NKTKLN/eink-environment-clock/firmware/src/epd_font5x7.h

/*
 * Classic 5x7 fixed-width bitmap font from Adafruit-GFX (glcdfont.c),
 * the same font the original Arduino sketch used. Each glyph is 5 column
 * bytes, bit 0 = top row. Index 95 is the degree sign.
 */
#pragma once

#include <stdint.h>

#define FONT5X7_DEGREE_INDEX 95

static const uint8_t font5x7[96][5] = {
    { 0x00, 0x00, 0x00, 0x00, 0x00 }, /*   */
    { 0x00, 0x00, 0x5F, 0x00, 0x00 }, /* ! */
    { 0x00, 0x07, 0x00, 0x07, 0x00 }, /* " */
    { 0x14, 0x7F, 0x14, 0x7F, 0x14 }, /* # */
    { 0x24, 0x2A, 0x7F, 0x2A, 0x12 }, /* $ */
    { 0x23, 0x13, 0x08, 0x64, 0x62 }, /* % */
    { 0x36, 0x49, 0x56, 0x20, 0x50 }, /* & */
    { 0x00, 0x08, 0x07, 0x03, 0x00 }, /* ' */
    { 0x00, 0x1C, 0x22, 0x41, 0x00 }, /* ( */
    { 0x00, 0x41, 0x22, 0x1C, 0x00 }, /* ) */
    { 0x2A, 0x1C, 0x7F, 0x1C, 0x2A }, /* asterisk */
    { 0x08, 0x08, 0x3E, 0x08, 0x08 }, /* + */
    { 0x00, 0x80, 0x70, 0x30, 0x00 }, /* , */
    { 0x08, 0x08, 0x08, 0x08, 0x08 }, /* - */
    { 0x00, 0x00, 0x60, 0x60, 0x00 }, /* . */
    { 0x20, 0x10, 0x08, 0x04, 0x02 }, /* / */
    { 0x3E, 0x51, 0x49, 0x45, 0x3E }, /* 0 */
    { 0x00, 0x42, 0x7F, 0x40, 0x00 }, /* 1 */
    { 0x72, 0x49, 0x49, 0x49, 0x46 }, /* 2 */
    { 0x21, 0x41, 0x49, 0x4D, 0x33 }, /* 3 */
    { 0x18, 0x14, 0x12, 0x7F, 0x10 }, /* 4 */
    { 0x27, 0x45, 0x45, 0x45, 0x39 }, /* 5 */
    { 0x3C, 0x4A, 0x49, 0x49, 0x31 }, /* 6 */
    { 0x41, 0x21, 0x11, 0x09, 0x07 }, /* 7 */
    { 0x36, 0x49, 0x49, 0x49, 0x36 }, /* 8 */
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
    { 0x44, 0x64, 0x54, 0x4C, 0x44 }, /* z */
    { 0x00, 0x08, 0x36, 0x41, 0x00 }, /* { */
    { 0x00, 0x00, 0x77, 0x00, 0x00 }, /* | */
    { 0x00, 0x41, 0x36, 0x08, 0x00 }, /* } */
    { 0x02, 0x01, 0x02, 0x04, 0x02 }, /* ~ */
    { 0x06, 0x0F, 0x09, 0x0F, 0x06 }, /* degree */
};
