NKTKLN/eink-environment-clock/firmware/src/net_time.c

#include "net_time.h"

#include <stdatomic.h>
#include <string.h>

#include "esp_event.h"
#include "esp_log.h"
#include "esp_netif.h"
#include "esp_sntp.h"
#include "esp_wifi.h"
#include "nvs_flash.h"

#include "app_config.h"

static const char *TAG = "net_time";

static atomic_bool s_synced;
static bool s_sntp_started;

static void on_time_sync(struct timeval *tv)
{
    (void)tv;
    ESP_LOGI(TAG, "time synchronized via SNTP");
    atomic_store(&s_synced, true);
}

static void start_sntp_once(void)
{
    if (s_sntp_started) {
        return;
    }
    s_sntp_started = true;

    esp_sntp_setoperatingmode(ESP_SNTP_OPMODE_POLL);
    esp_sntp_setservername(0, NTP_SERVER);
    sntp_set_time_sync_notification_cb(on_time_sync);
    sntp_set_sync_interval((uint32_t)TIME_SYNC_INTERVAL_S * 1000);
    esp_sntp_init();
}

static void wifi_event_handler(void *arg, esp_event_base_t base,
                               int32_t event_id, void *data)
{
    if (base == WIFI_EVENT && event_id == WIFI_EVENT_STA_START) {
        esp_wifi_connect();
    } else if (base == WIFI_EVENT && event_id == WIFI_EVENT_STA_DISCONNECTED) {
        ESP_LOGW(TAG, "Wi-Fi disconnected, reconnecting");
        esp_wifi_connect();
    } else if (base == IP_EVENT && event_id == IP_EVENT_STA_GOT_IP) {
        ip_event_got_ip_t *event = (ip_event_got_ip_t *)data;
        ESP_LOGI(TAG, "got IP: " IPSTR, IP2STR(&event->ip_info.ip));
        start_sntp_once();
    }
}

esp_err_t net_time_start(void)
{
    esp_err_t err = nvs_flash_init();
    if (err == ESP_ERR_NVS_NO_FREE_PAGES ||
        err == ESP_ERR_NVS_NEW_VERSION_FOUND) {
        ESP_ERROR_CHECK(nvs_flash_erase());
        err = nvs_flash_init();
    }
    if (err != ESP_OK) {
        return err;
    }

    ESP_ERROR_CHECK(esp_netif_init());
    ESP_ERROR_CHECK(esp_event_loop_create_default());
    esp_netif_create_default_wifi_sta();

    wifi_init_config_t init_cfg = WIFI_INIT_CONFIG_DEFAULT();
    ESP_ERROR_CHECK(esp_wifi_init(&init_cfg));

    ESP_ERROR_CHECK(esp_event_handler_register(WIFI_EVENT, ESP_EVENT_ANY_ID,
                                               wifi_event_handler, NULL));
    ESP_ERROR_CHECK(esp_event_handler_register(IP_EVENT, IP_EVENT_STA_GOT_IP,
                                               wifi_event_handler, NULL));

    wifi_config_t wifi_cfg = { 0 };
    strlcpy((char *)wifi_cfg.sta.ssid, WIFI_SSID, sizeof(wifi_cfg.sta.ssid));
    strlcpy((char *)wifi_cfg.sta.password, WIFI_PASSWORD,
            sizeof(wifi_cfg.sta.password));

    ESP_ERROR_CHECK(esp_wifi_set_mode(WIFI_MODE_STA));
    ESP_ERROR_CHECK(esp_wifi_set_config(WIFI_IF_STA, &wifi_cfg));
    return esp_wifi_start();
}

bool net_time_take_synced(void)
{
    return atomic_exchange(&s_synced, false);
}
